pashutk/chocofi/images/IMG_7035.jpg

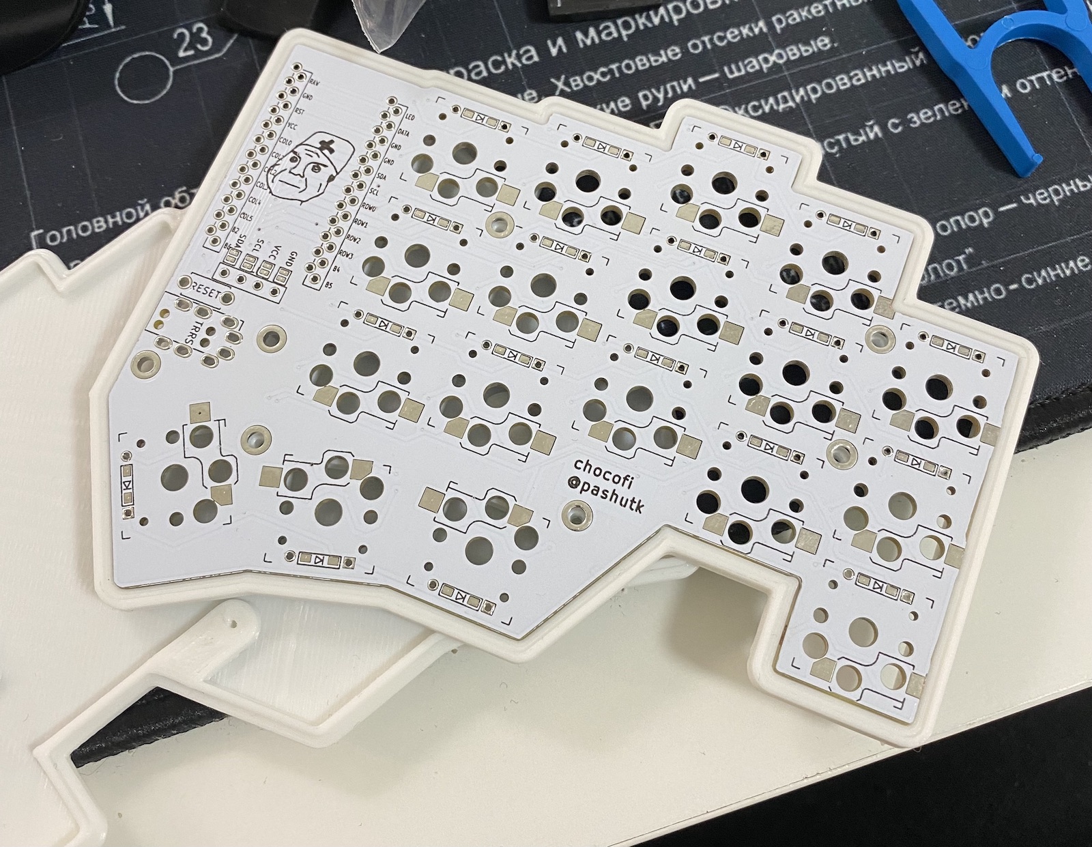
images/IMG_7035.jpg
