pashutk/chocofi/images/IMG_7057.jpeg

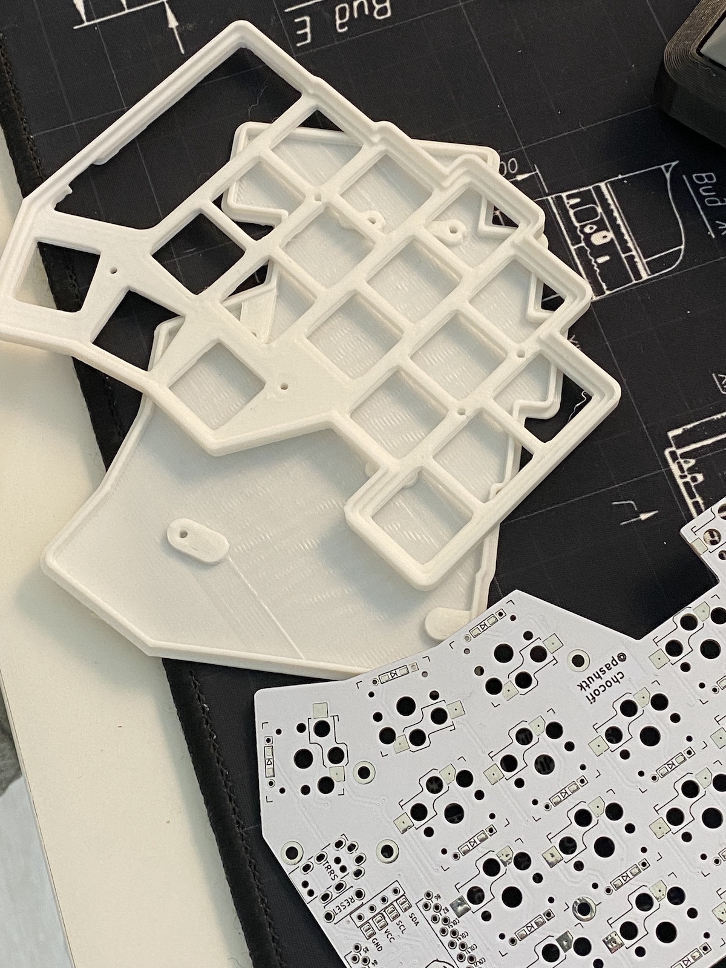
images/IMG_7057.jpeg
