pashutk/chocofi/images/IMG_7062.jpeg

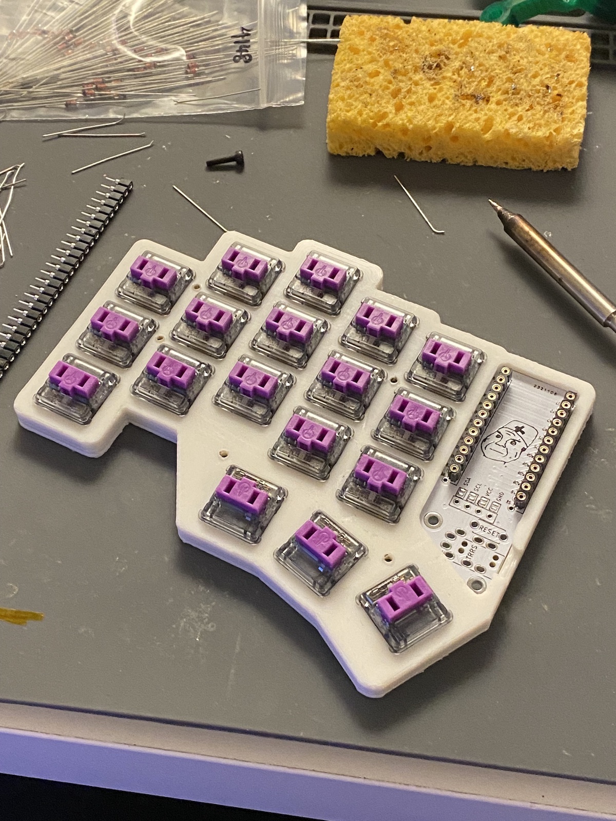
images/IMG_7062.jpeg
