pashutk/chocofi/images/IMG_7070.jpeg

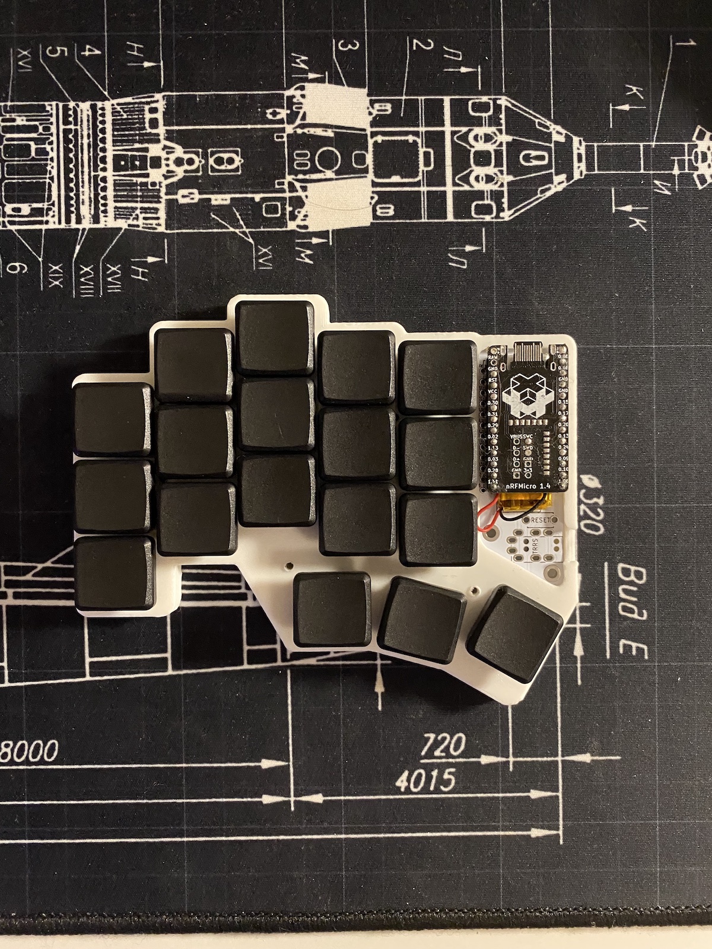
images/IMG_7070.jpeg
